rrguardo/WiFi-Water-Level-S1/images/btc_donations.png

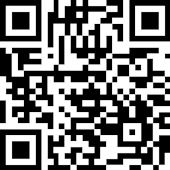
images/btc_donations.png
