rrguardo/WiFi-Water-Level-S1/images/SunBuddyC3_V6_PCB_Roles.png

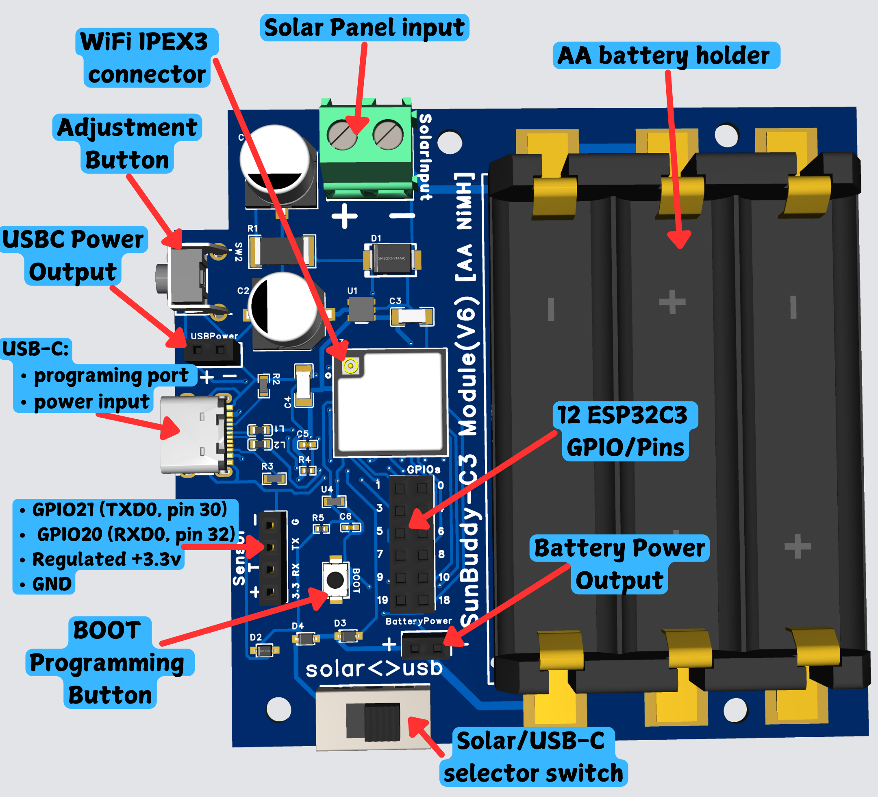
images/SunBuddyC3_V6_PCB_Roles.png
